Jackadminx/Keyboard_nano/IMG/wiki/flash/2.jpg

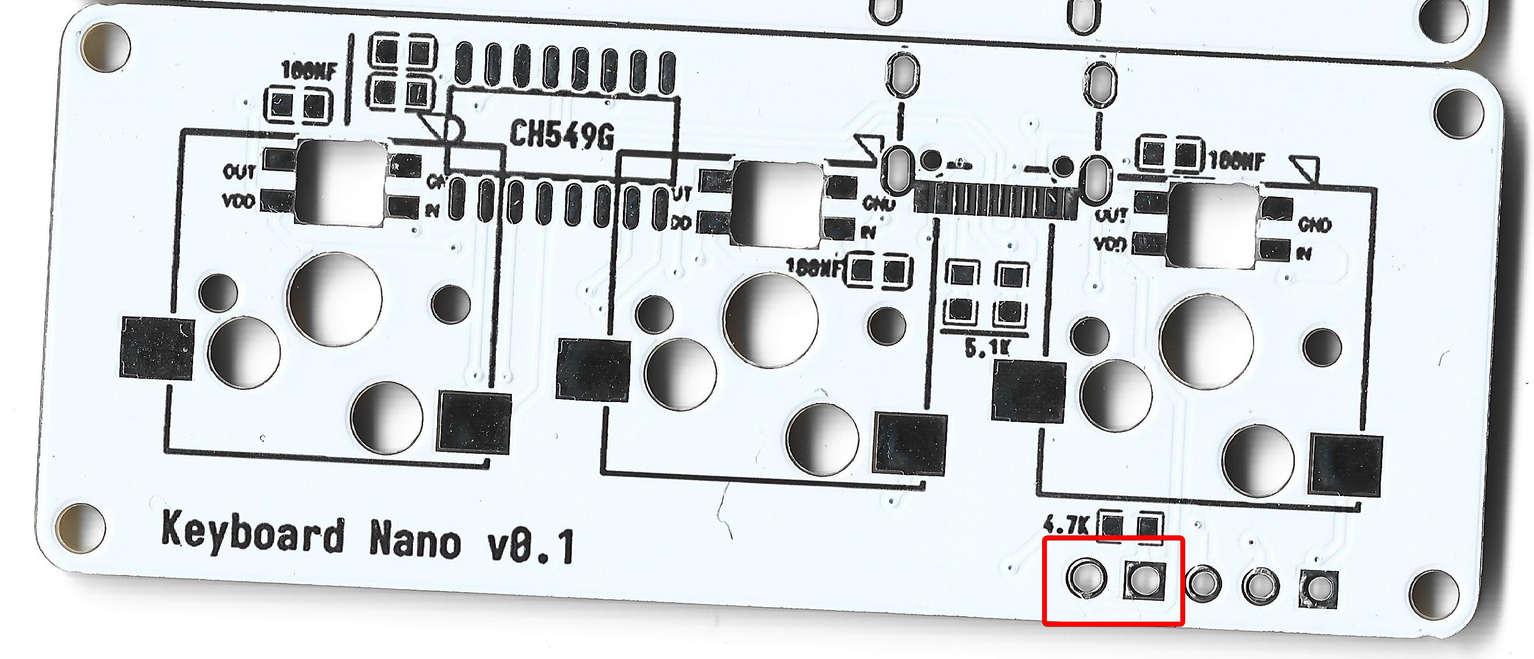
IMG/wiki/flash/2.jpg
