Jackadminx/Keyboard_nano/IMG/wiki/flash/4.jpg

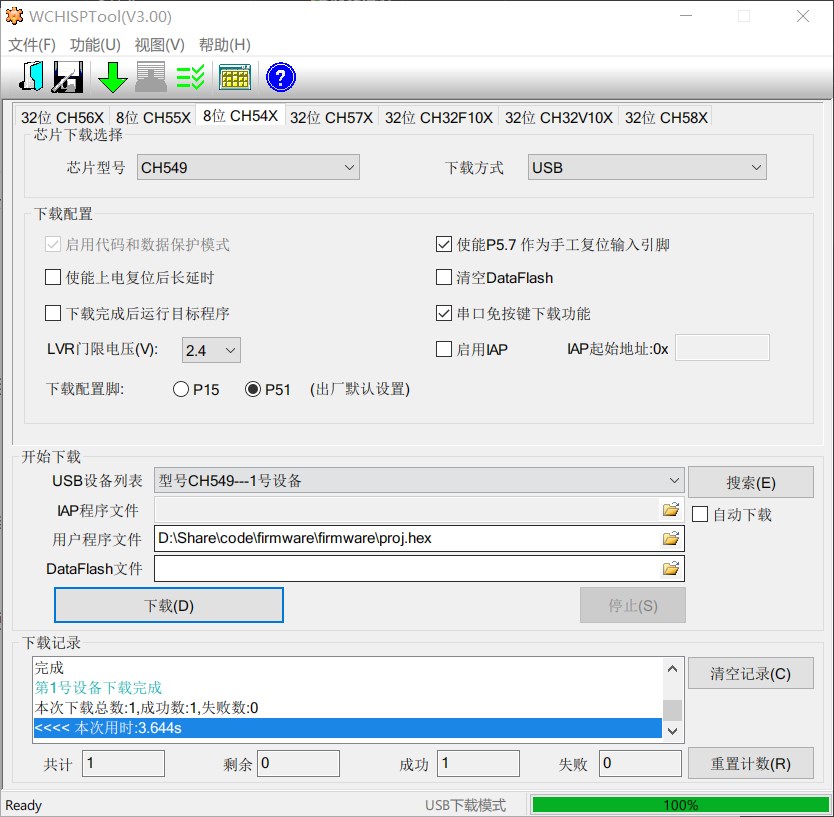
IMG/wiki/flash/4.jpg
